dczia/Defcon27-Badge/Hardware/Images/code-back.png

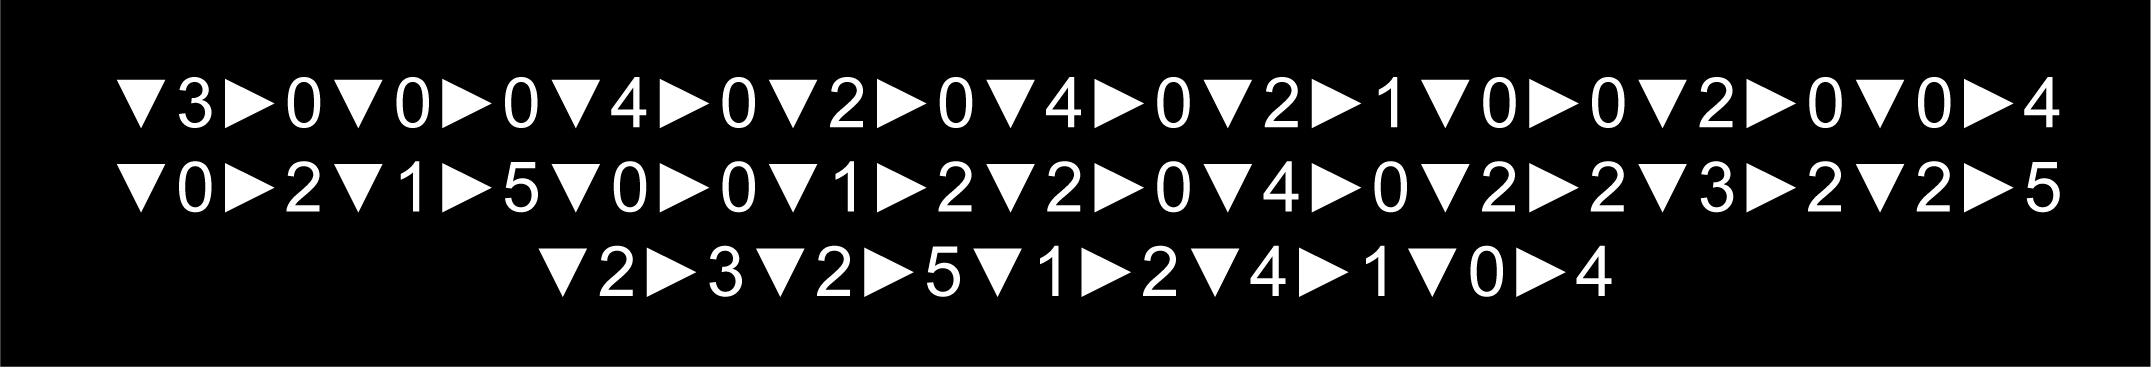
Hardware/Images/code-back.png
