dczia/Defcon27-Badge/Hardware/Images/copper-border.png

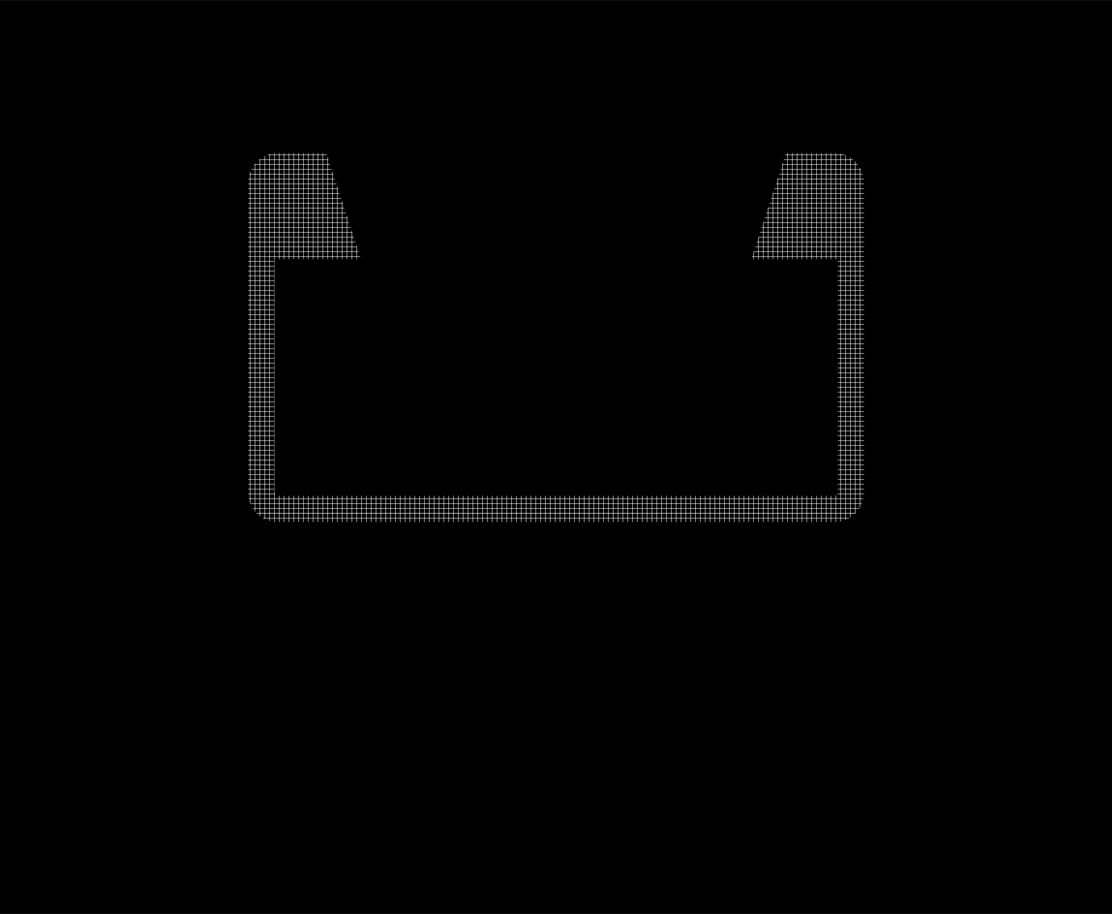
Hardware/Images/copper-border.png
