dczia/Defcon27-Badge/Hardware/Images/credits.png

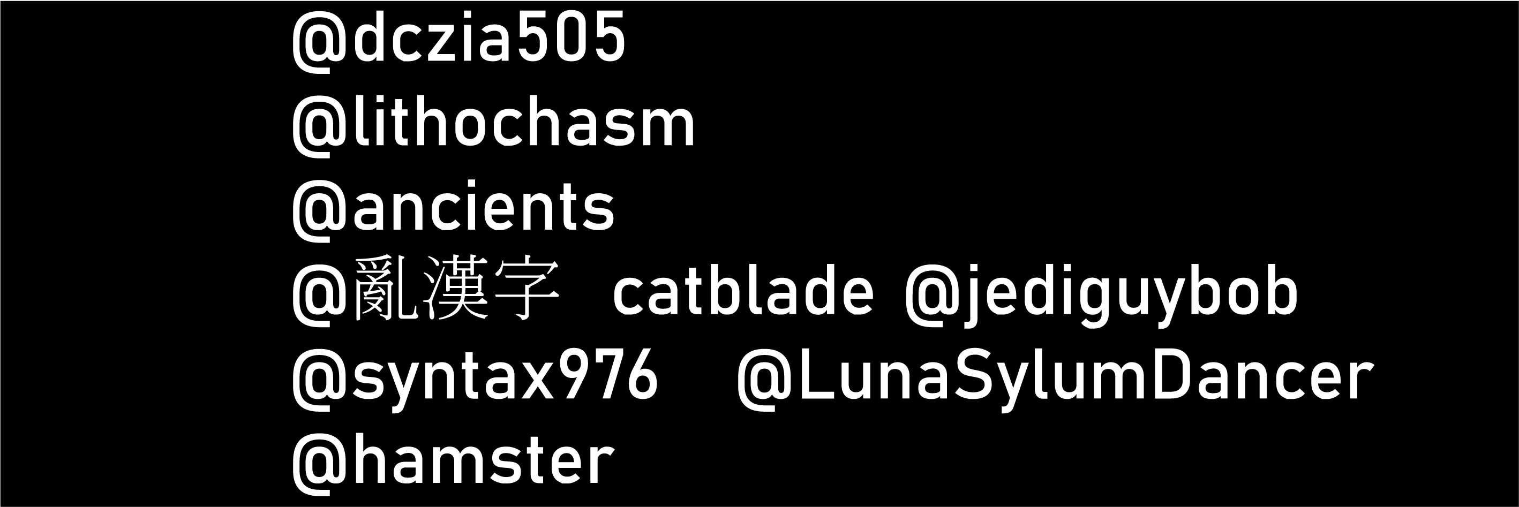
Hardware/Images/credits.png
