dczia/Defcon27-Badge/Hardware/Images/dczia-text.png

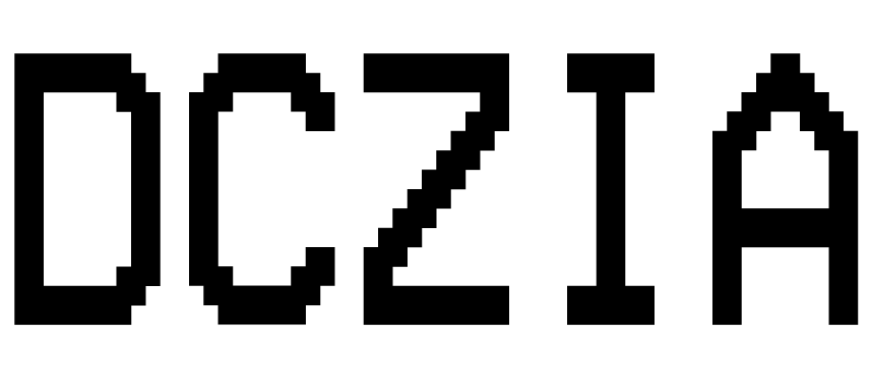
Hardware/Images/dczia-text.png
