dczia/Defcon27-Badge/Hardware/Images/halftone1.png

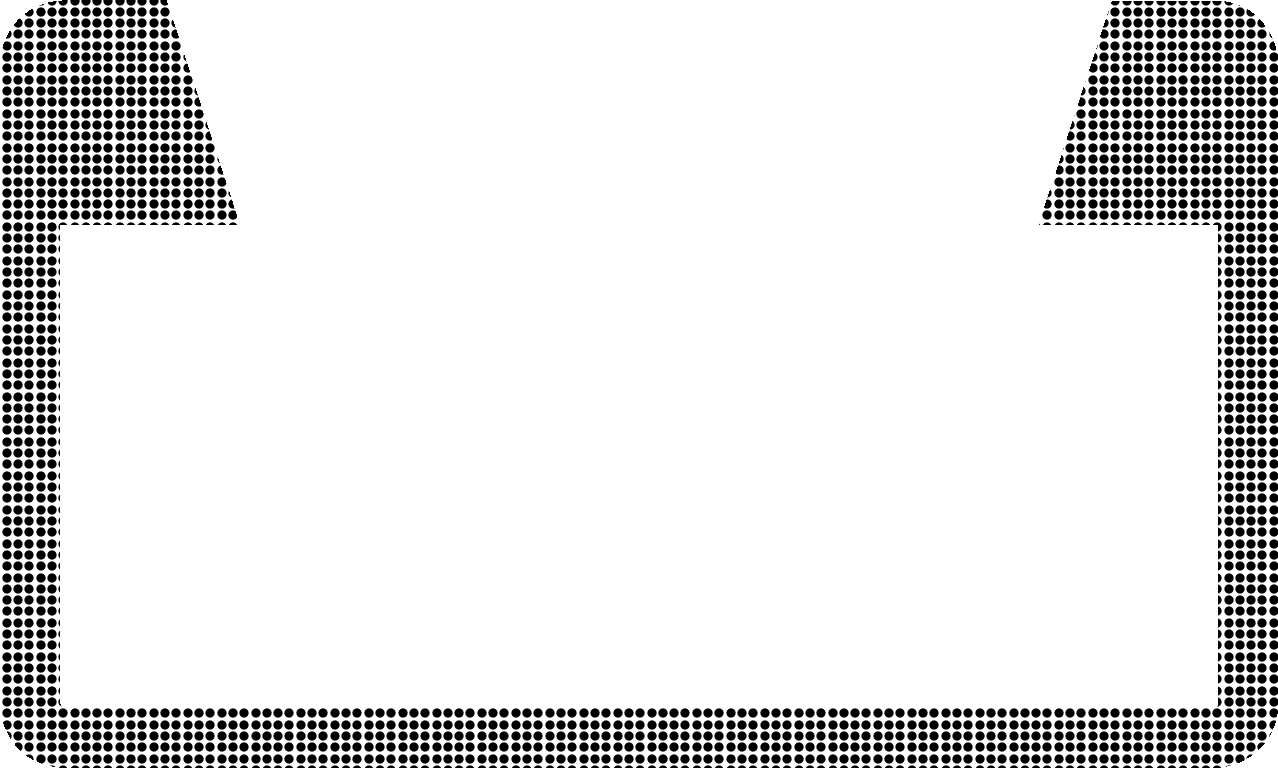
Hardware/Images/halftone1.png
