dczia/Defcon27-Badge/Hardware/Images/laser-theremin-back-1.png

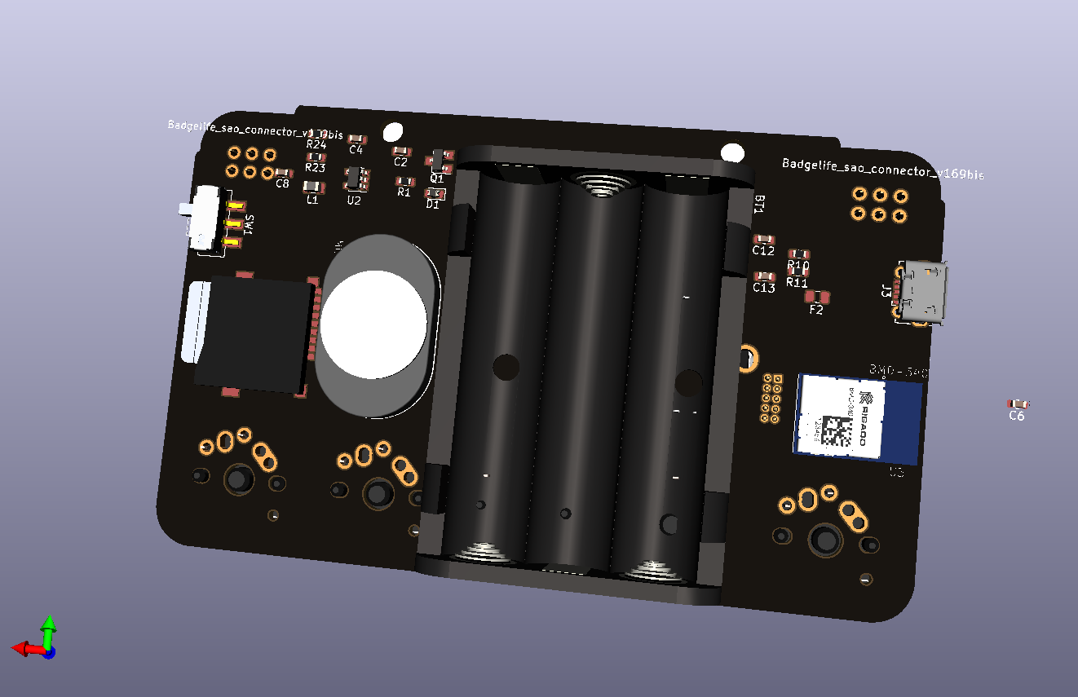
Hardware/Images/laser-theremin-back-1.png
