dczia/Defcon27-Badge/Hardware/Images/laser-theremin-back-2.png

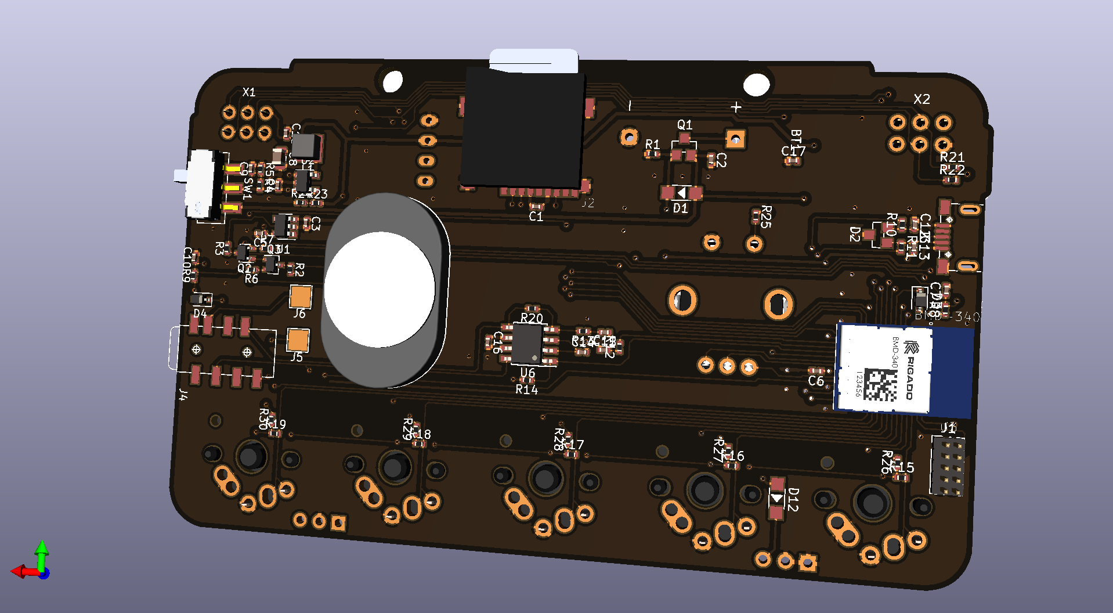
Hardware/Images/laser-theremin-back-2.png
