dczia/Defcon27-Badge/Hardware/Images/laser-theremin-back-3.png

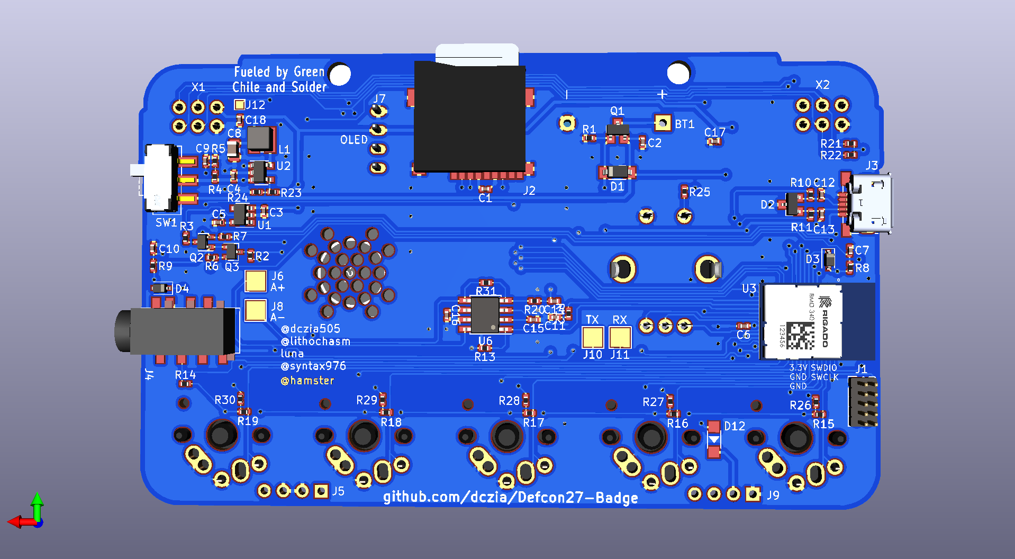
Hardware/Images/laser-theremin-back-3.png
