dczia/Defcon27-Badge/Hardware/Images/laser-theremin-back-4.png

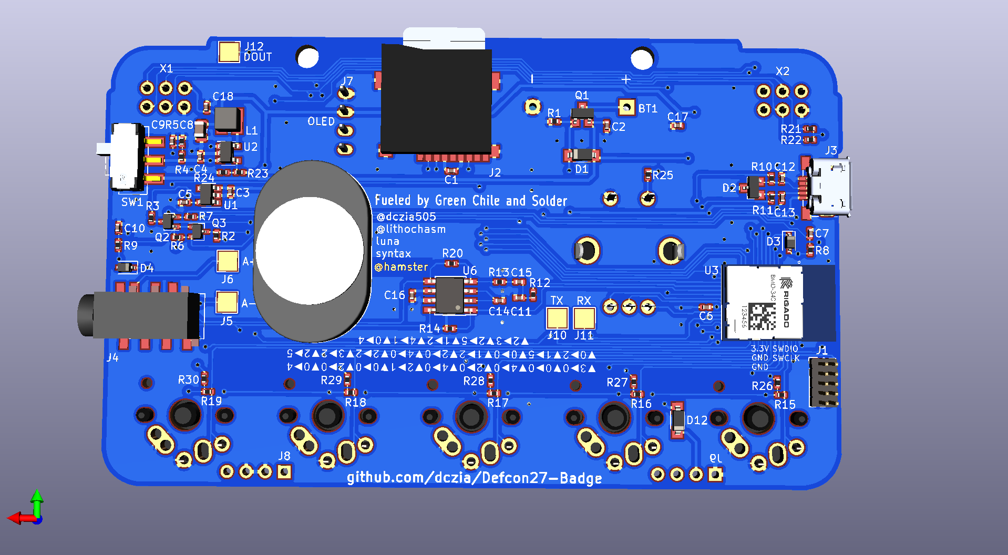
Hardware/Images/laser-theremin-back-4.png
