dczia/Defcon27-Badge/Hardware/Images/laser-theremin-back-ray-3.png

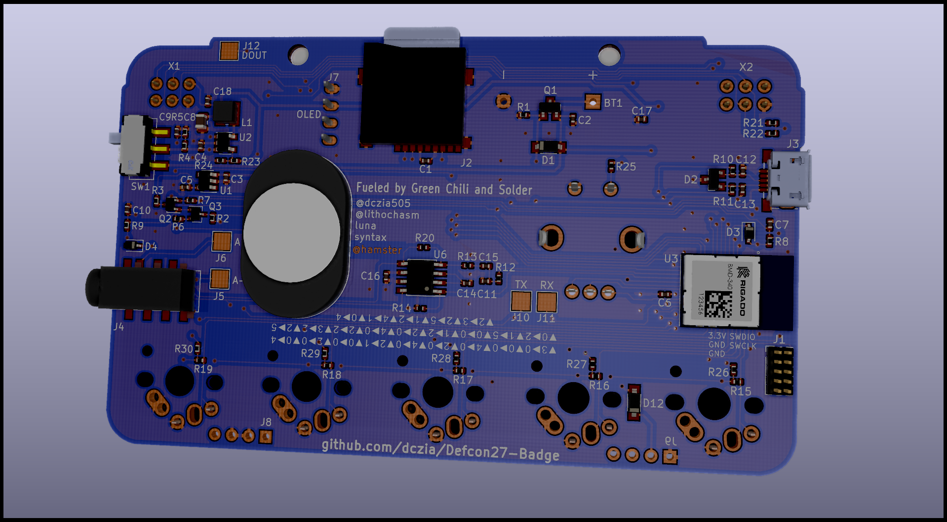
Hardware/Images/laser-theremin-back-ray-3.png
