dczia/Defcon27-Badge/Hardware/Images/laser-theremin-front-1.png

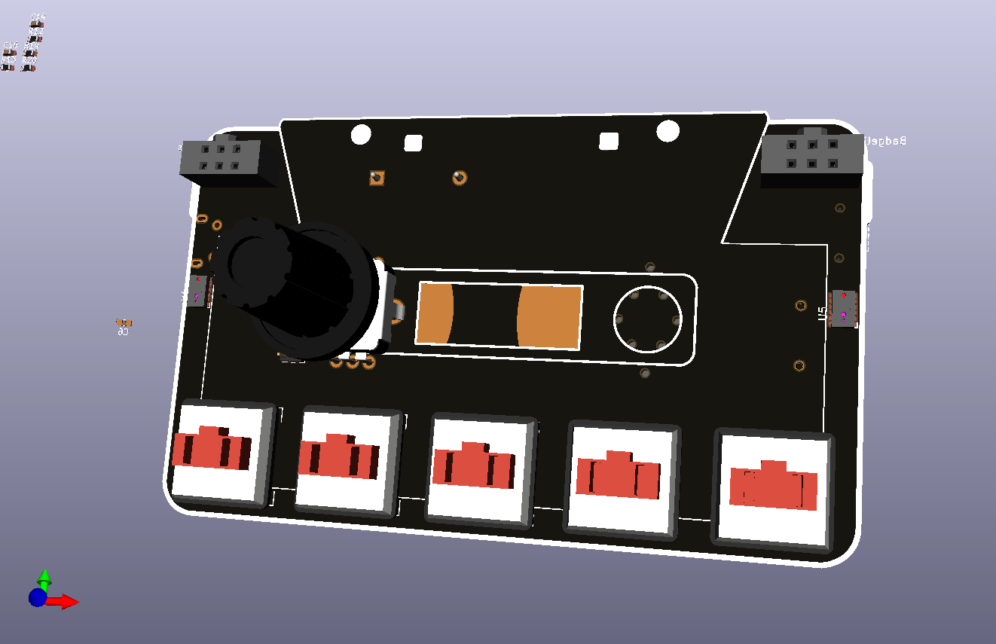
Hardware/Images/laser-theremin-front-1.png
