dczia/Defcon27-Badge/Hardware/Images/laser-theremin-front-2.png

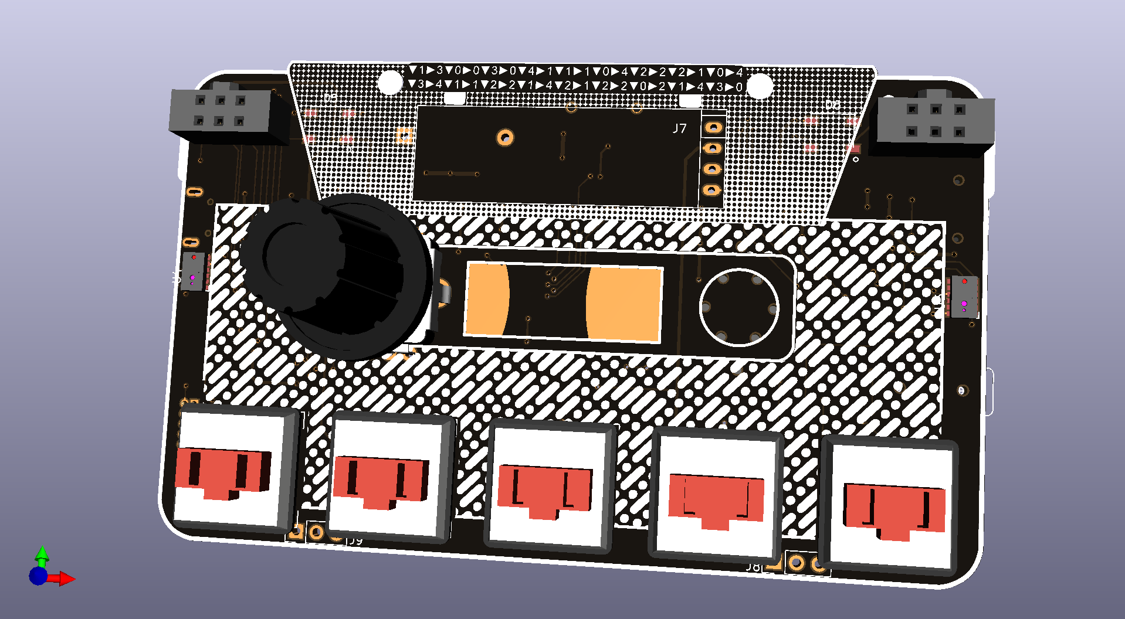
Hardware/Images/laser-theremin-front-2.png
