dczia/Defcon27-Badge/Hardware/Images/laser-theremin-front-3.png

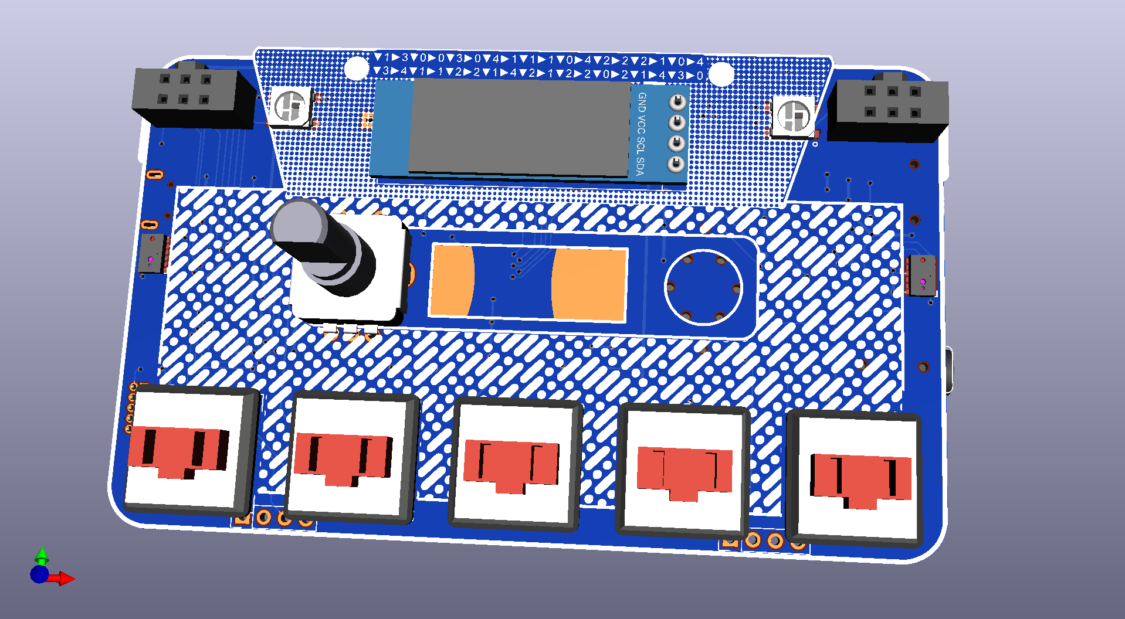
Hardware/Images/laser-theremin-front-3.png
