dczia/Defcon27-Badge/Hardware/Images/laser-theremin-front-5.png

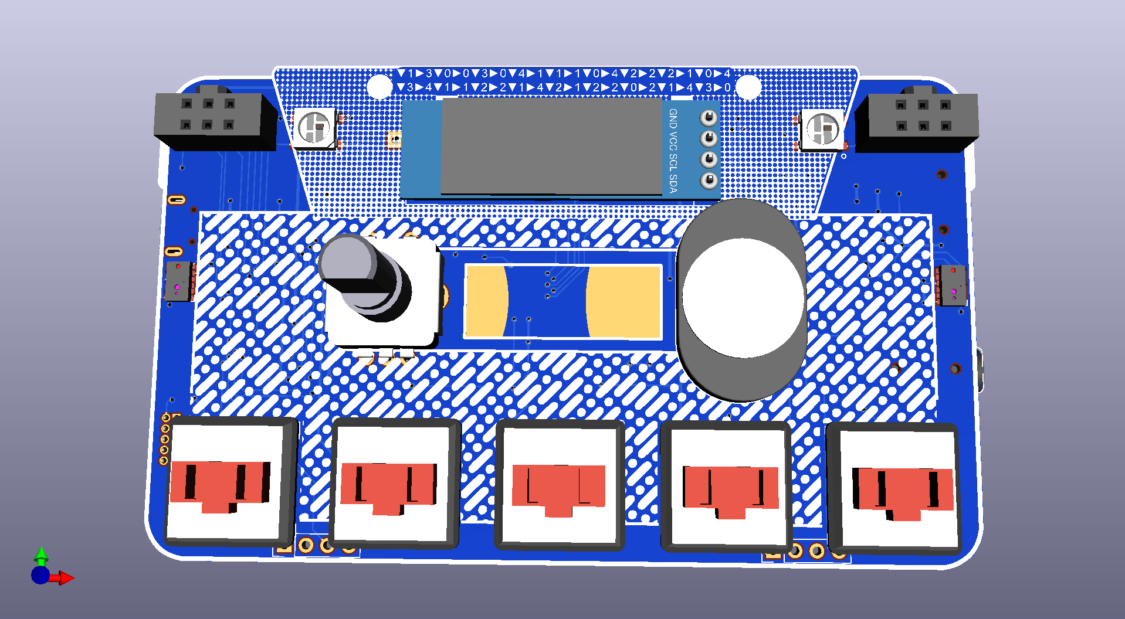
Hardware/Images/laser-theremin-front-5.png
