dczia/Defcon27-Badge/Hardware/Images/laser-theremin-front-ray-4.png

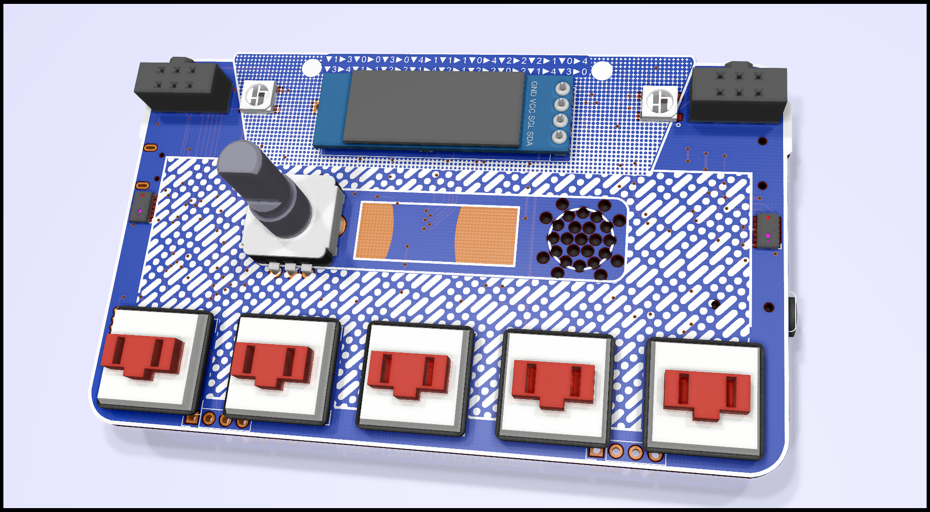
Hardware/Images/laser-theremin-front-ray-4.png
