dczia/Defcon27-Badge/Hardware/Images/laser-theremin-frontquarter-ray-3.png

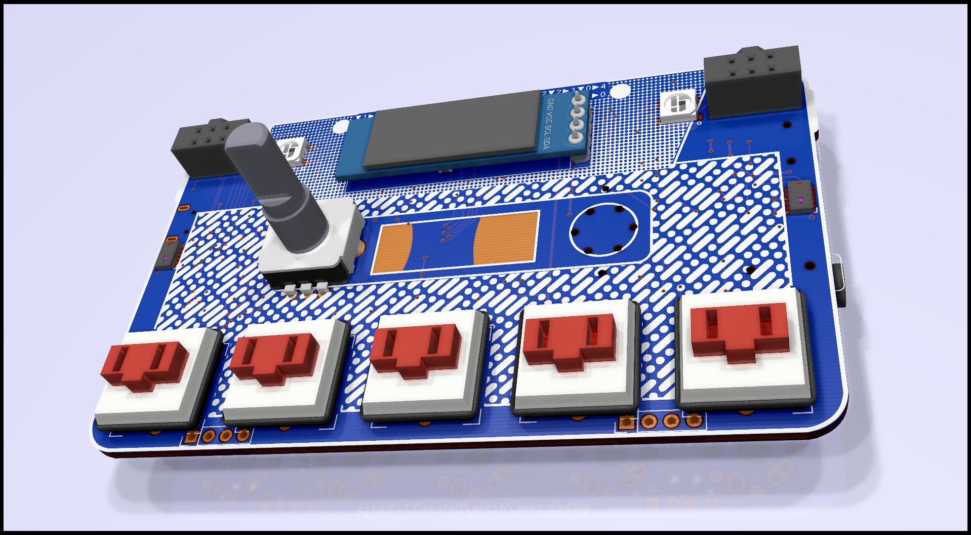
Hardware/Images/laser-theremin-frontquarter-ray-3.png
