dczia/Defcon27-Badge/Hardware/Images/mockup3.png

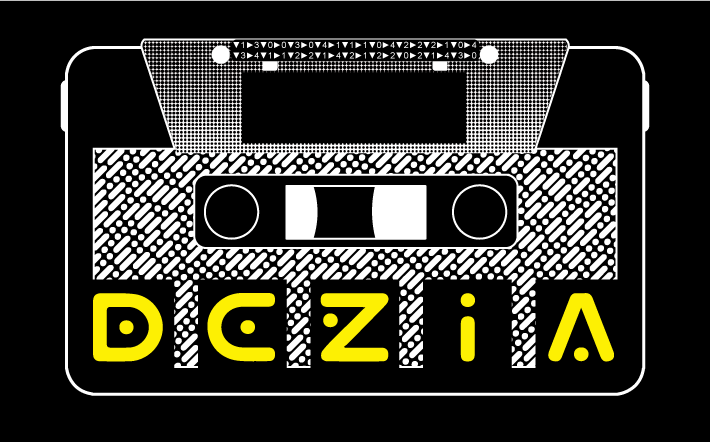
Hardware/Images/mockup3.png
