dczia/Defcon27-Badge/Hardware/Images/mockup.png

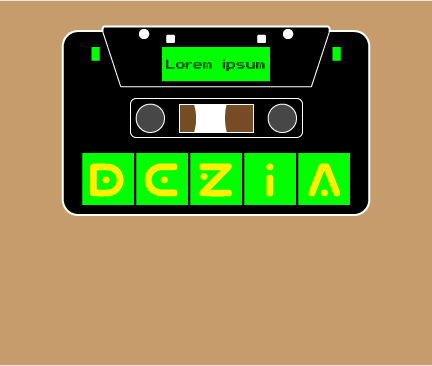
Hardware/Images/mockup.png
