dczia/Defcon27-Badge/Hardware/Images/silk-lines.png

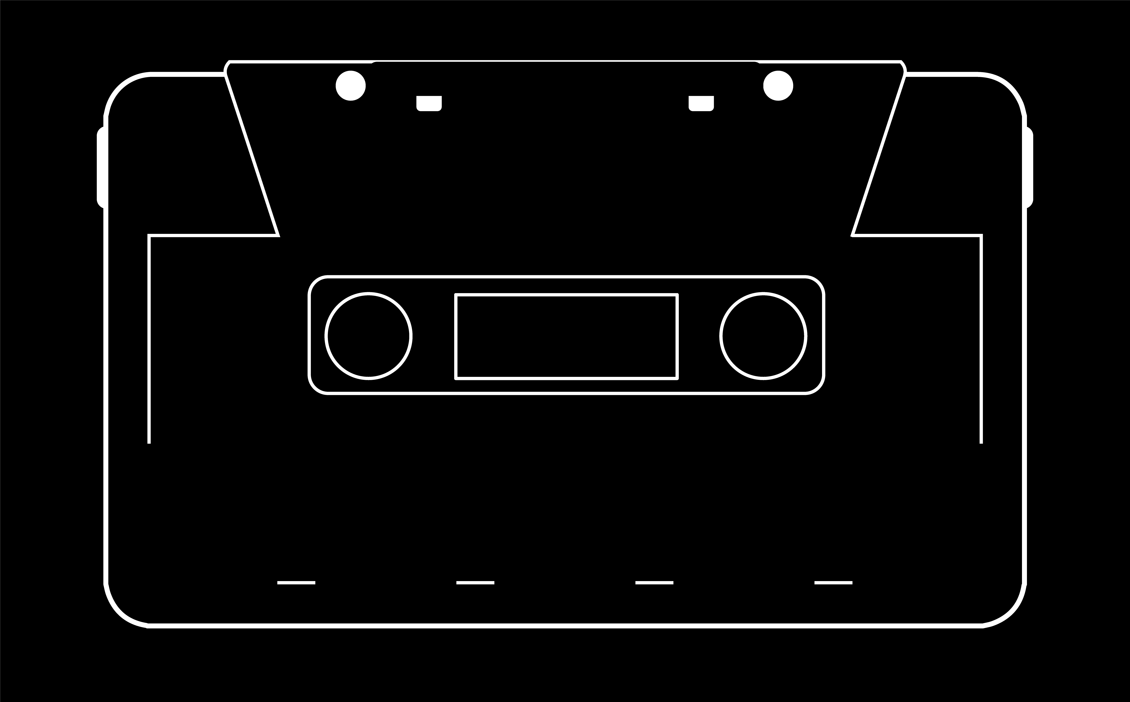
Hardware/Images/silk-lines.png
